tbutman/tilde-card/out/makerworld-sample/card-chrome.stl

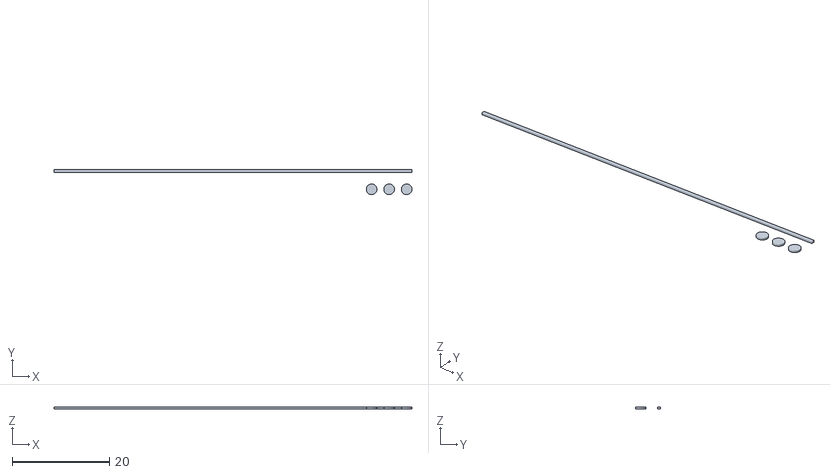
[picture p17: CAD file, 2026-10-07]
out/makerworld-sample/card-chrome.stl
73.6 x 5.20 x 0.4
