tbutman/tilde-card/makerworld/images/02-both-sides.png

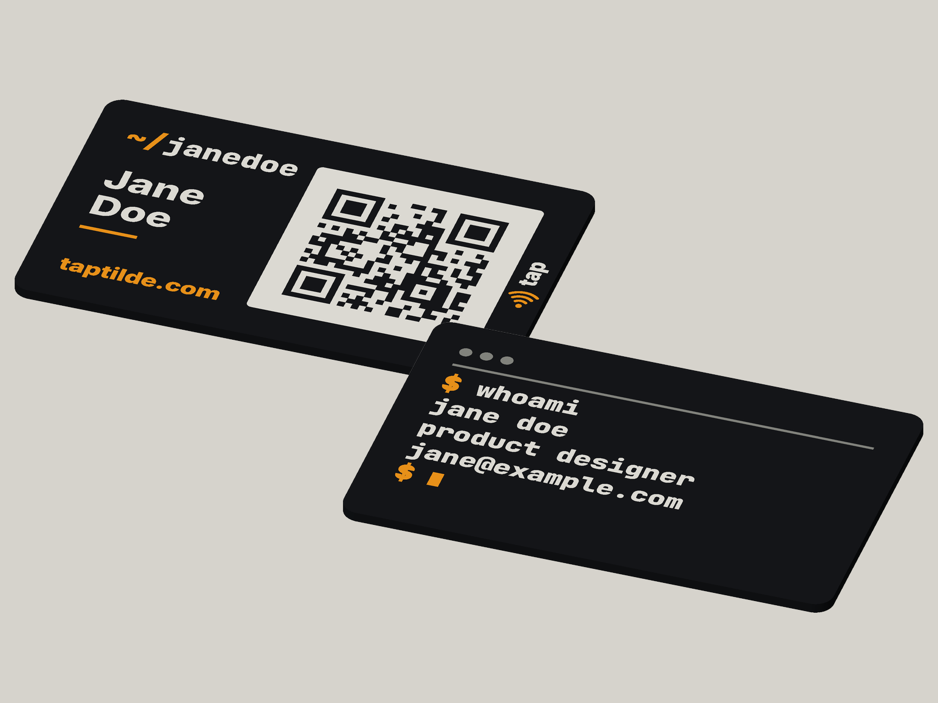
makerworld/images/02-both-sides.png
