tbutman/tilde-card/makerworld/images/05-sticker.png

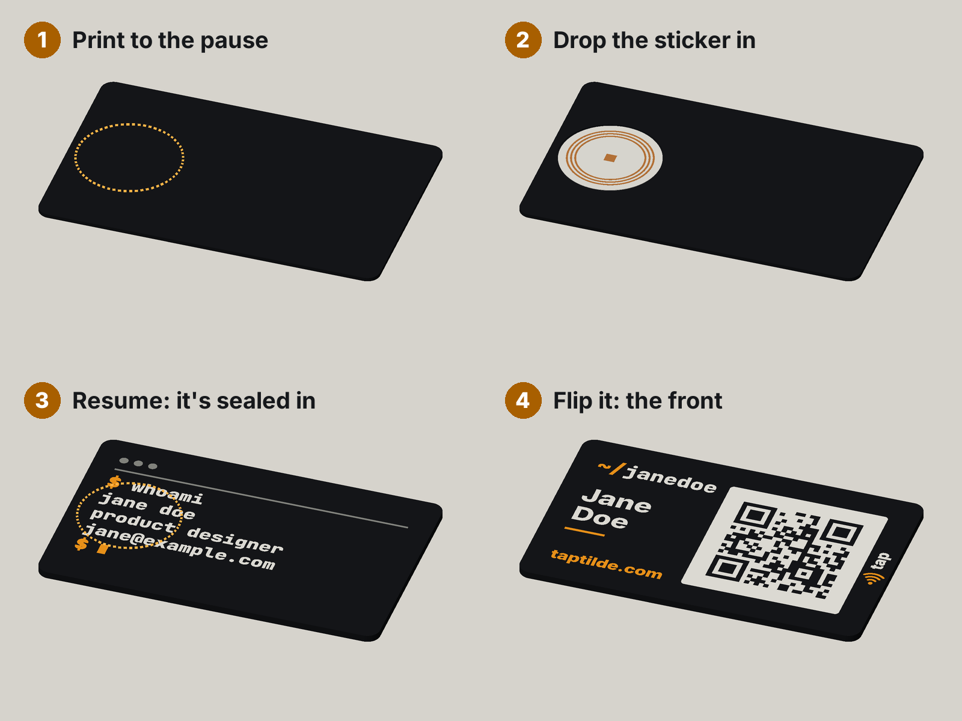
makerworld/images/05-sticker.png
