tbutman/tilde-card/makerworld/images/covers/cover-card-app.png

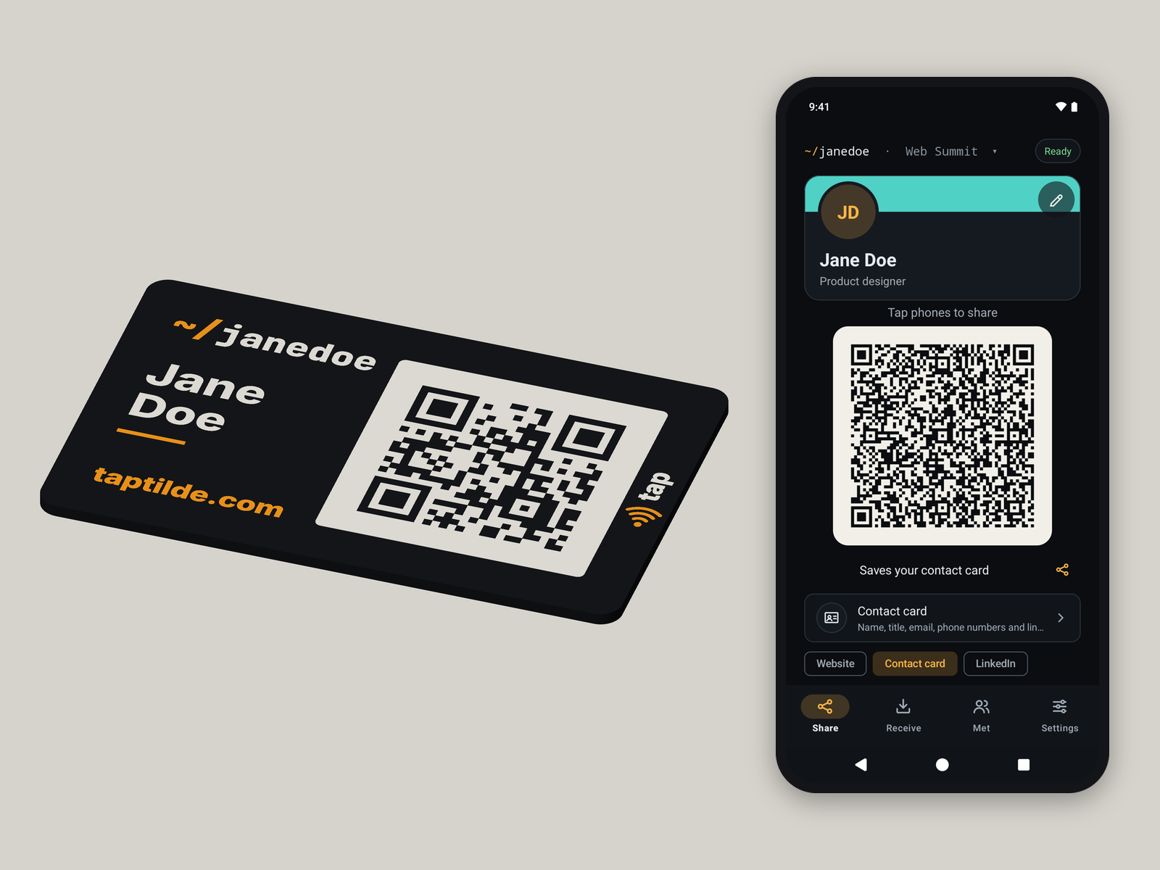
makerworld/images/covers/cover-card-app.png
