tbutman/tilde-card/makerworld/images/covers/cover-card-title-portrait.png

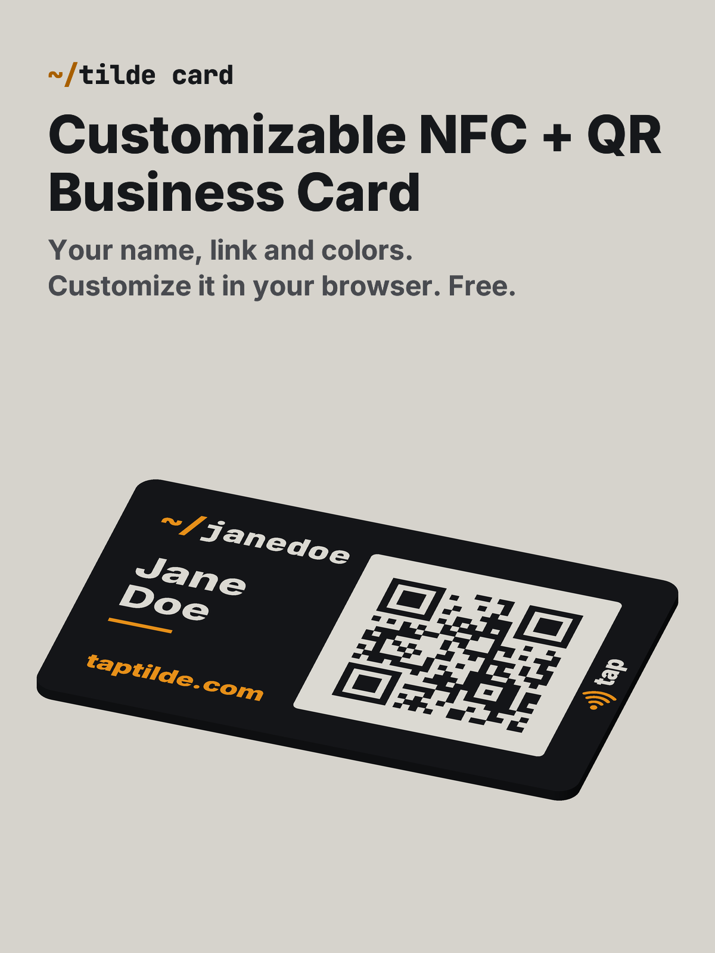
makerworld/images/covers/cover-card-title-portrait.png
