tbutman/tilde-card/makerworld/images/covers/cover-card-title.png

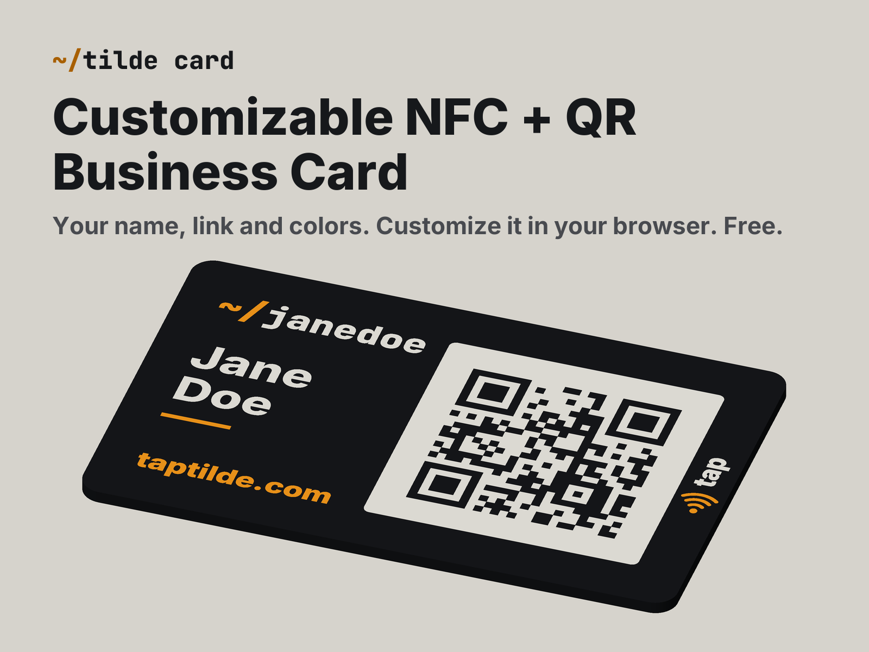
makerworld/images/covers/cover-card-title.png
