tbutman/tilde-card/makerworld/video/tilde-card.jpg

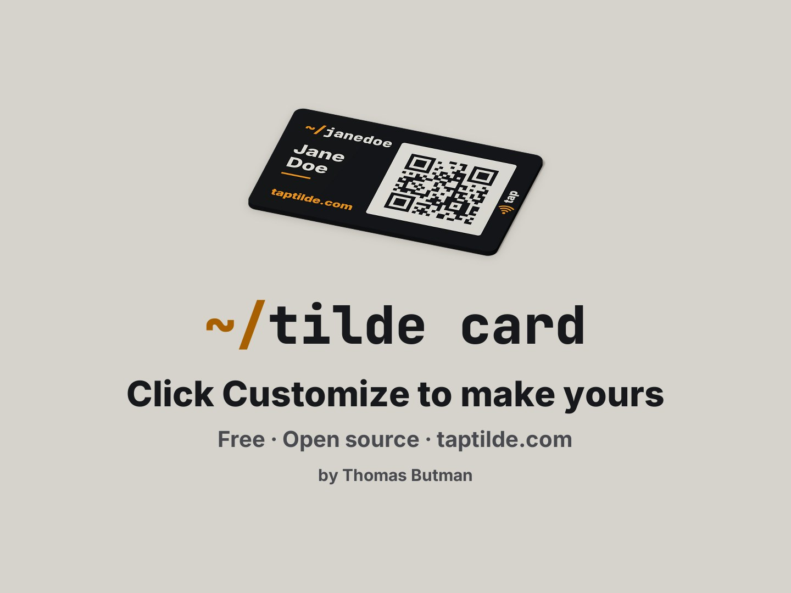
makerworld/video/tilde-card.jpg
