tbutman/tilde-card/out/makerworld-sample-qr-only-plain/card-back-surface.png

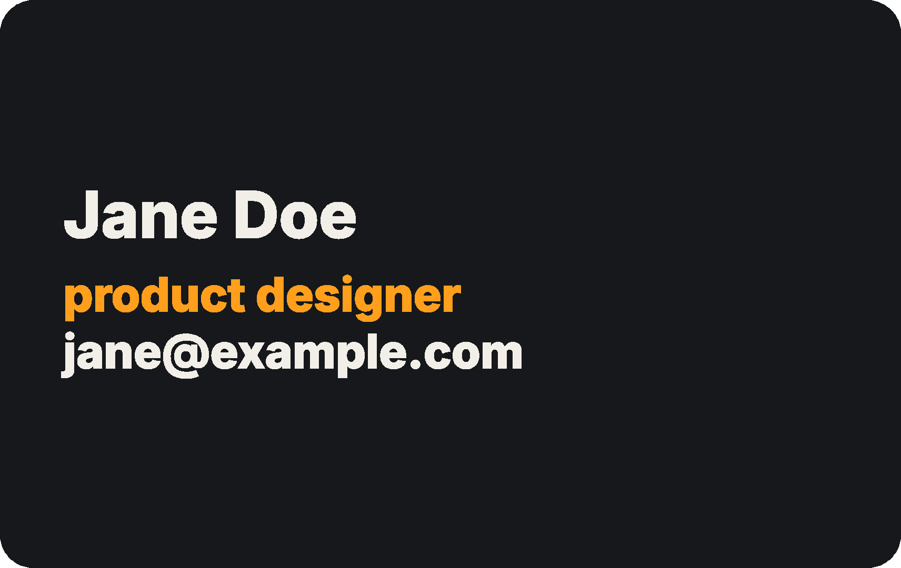
out/makerworld-sample-qr-only-plain/card-back-surface.png
